yohancsx/MinionsStereoCamera/Images/arducamScrews.PNG

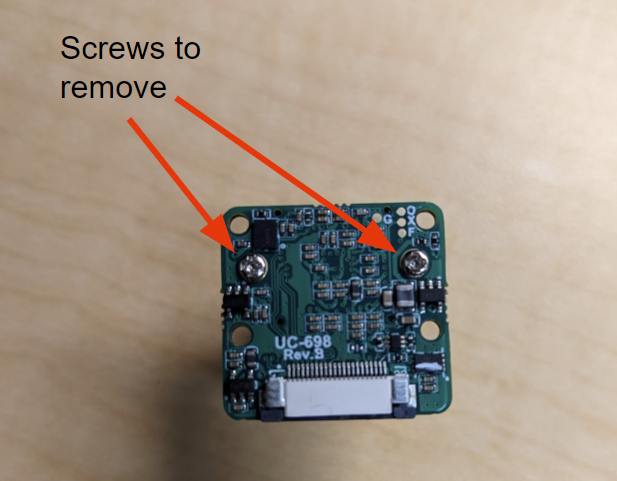
Images/arducamScrews.PNG
