yohancsx/MinionsStereoCamera/Images/cameraFilling.PNG

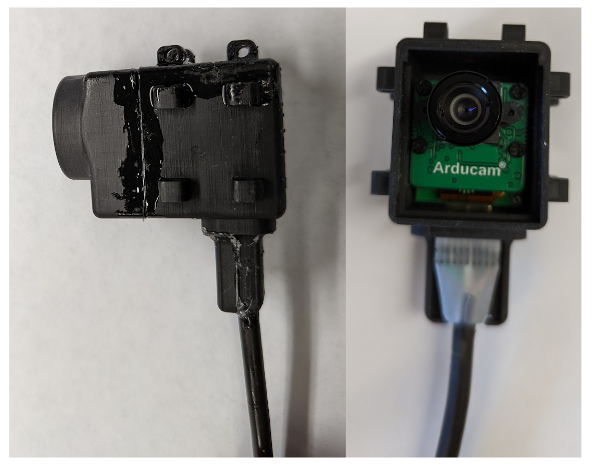
Images/cameraFilling.PNG
