yohancsx/MinionsStereoCamera/Images/housingDiagram.PNG

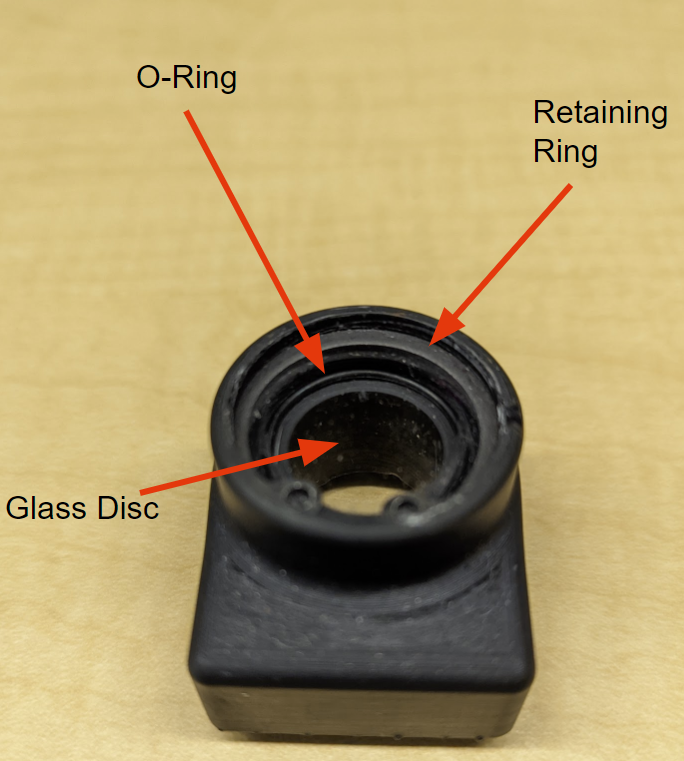
Images/housingDiagram.PNG
