yohancsx/MinionsStereoCamera/Images/lightFilling.PNG

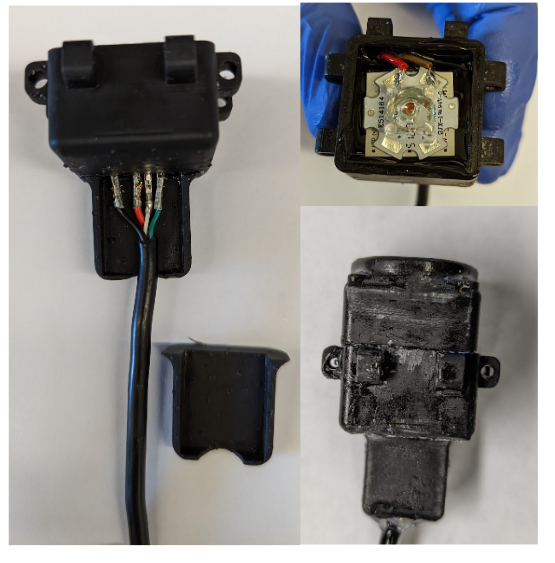
Images/lightFilling.PNG
