yohancsx/MinionsStereoCamera/Images/powerGroundDriver.PNG

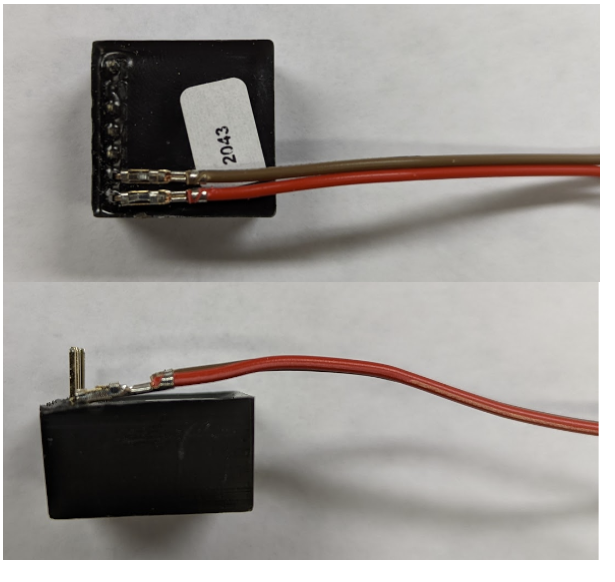
Images/powerGroundDriver.PNG
