yohancsx/MinionsStereoCamera/Images/PXL_20220421_215147885.jpg

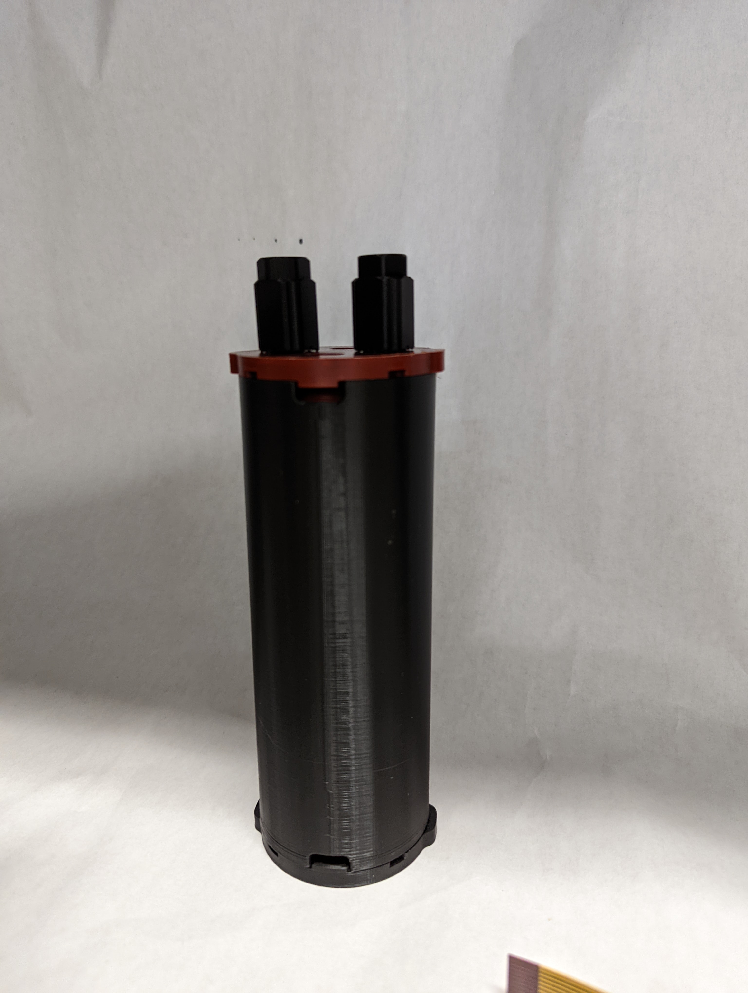
Images/PXL_20220421_215147885.jpg
