yohancsx/MinionsStereoCamera/Images/PXL_20220421_220706558.jpg

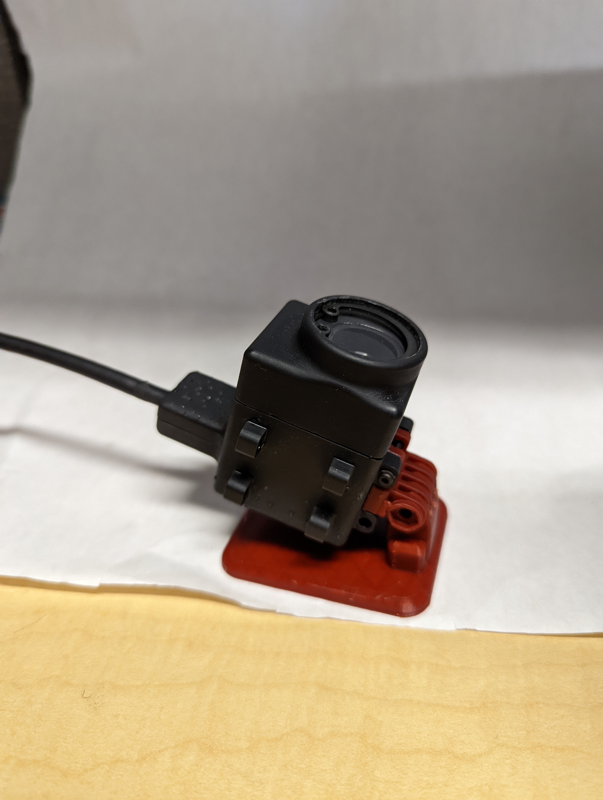
Images/PXL_20220421_220706558.jpg
