yohancsx/MinionsStereoCamera/Images/PXL_20220421_220925433.jpg

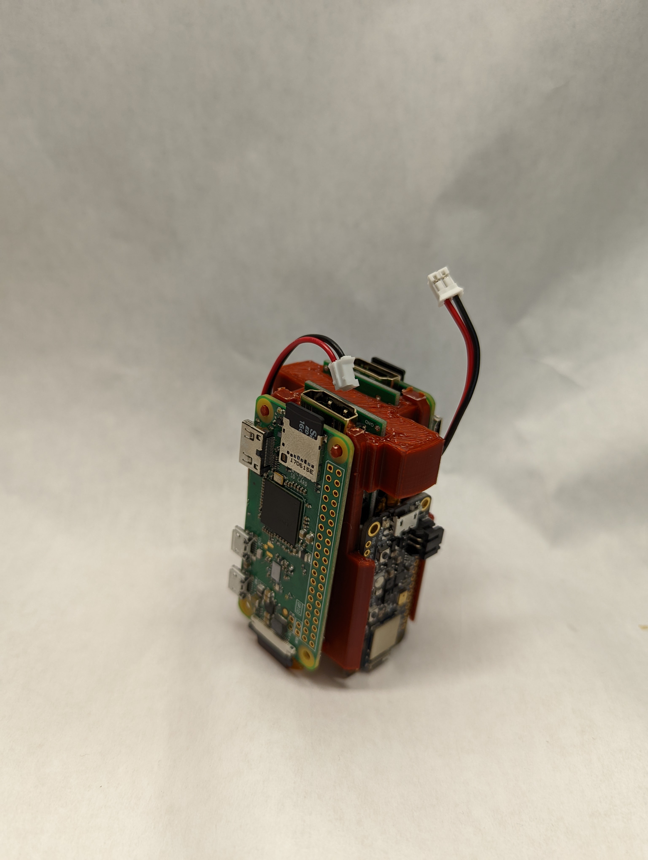
Images/PXL_20220421_220925433.jpg
