yohancsx/MinionsStereoCamera/Images/PXL_20220421_222905097.jpg

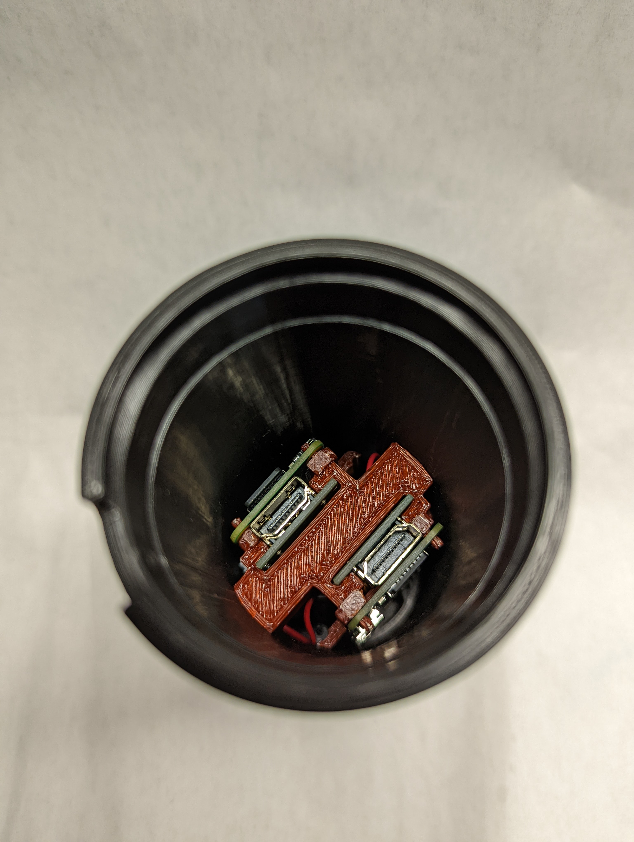
Images/PXL_20220421_222905097.jpg
