yohancsx/MinionsStereoCamera/Images/PXL_20220526_020410349.jpg

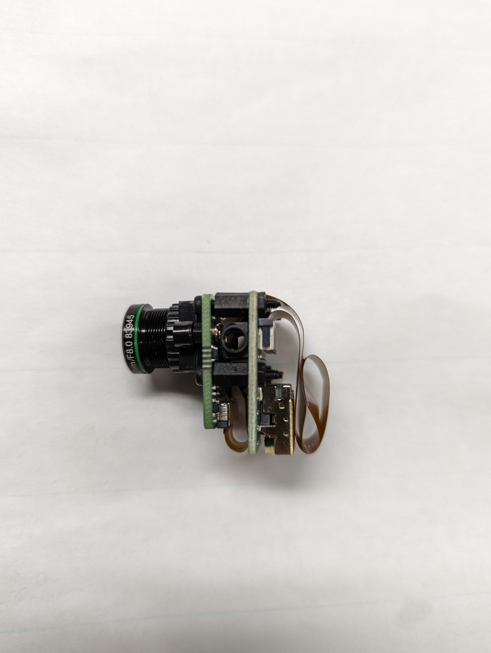
Images/PXL_20220526_020410349.jpg
