yohancsx/MinionsStereoCamera/Images/PXL_20220526_020418973.jpg

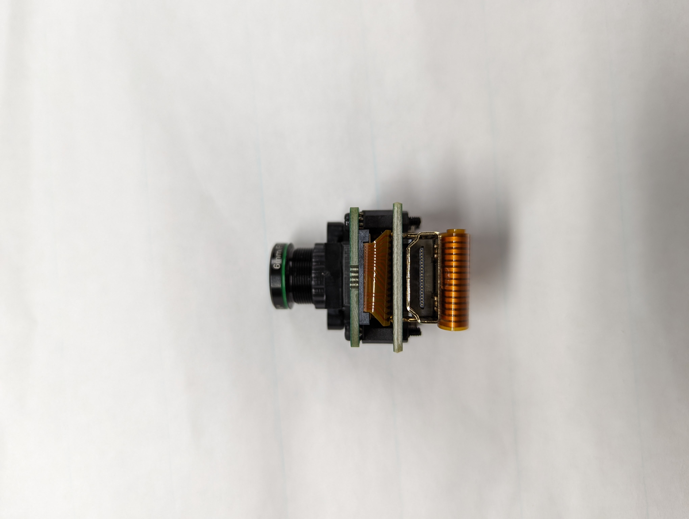
Images/PXL_20220526_020418973.jpg
