yohancsx/MinionsStereoCamera/Images/PXL_20220526_020445970.jpg

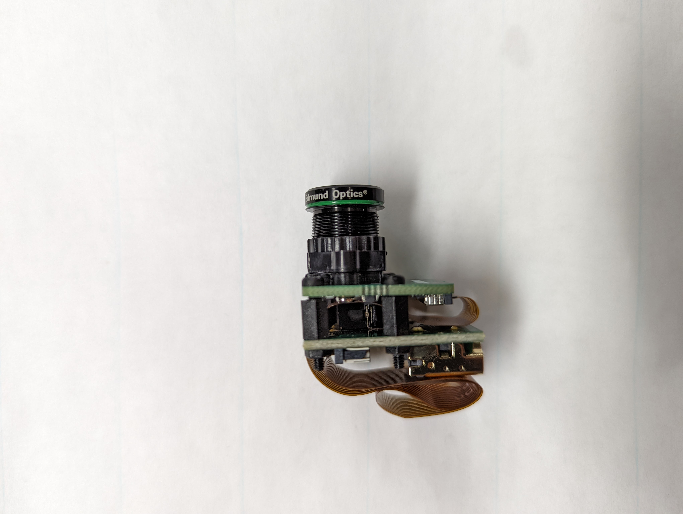
Images/PXL_20220526_020445970.jpg
