yohancsx/MinionsStereoCamera/Images/PXL_20220528_033501220.jpg

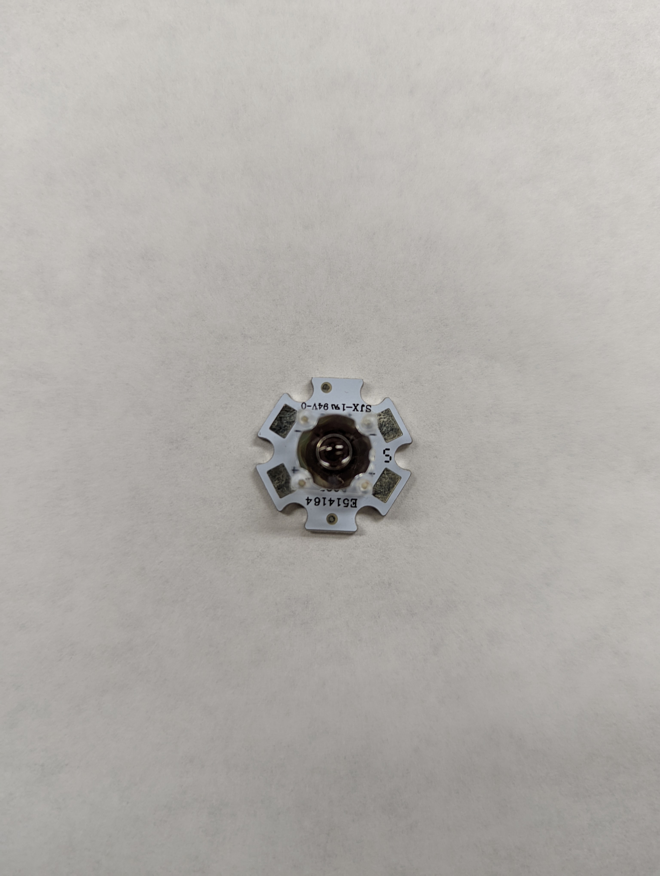
Images/PXL_20220528_033501220.jpg
