yohancsx/MinionsStereoCamera/Images/PXL_20220528_033528025.jpg

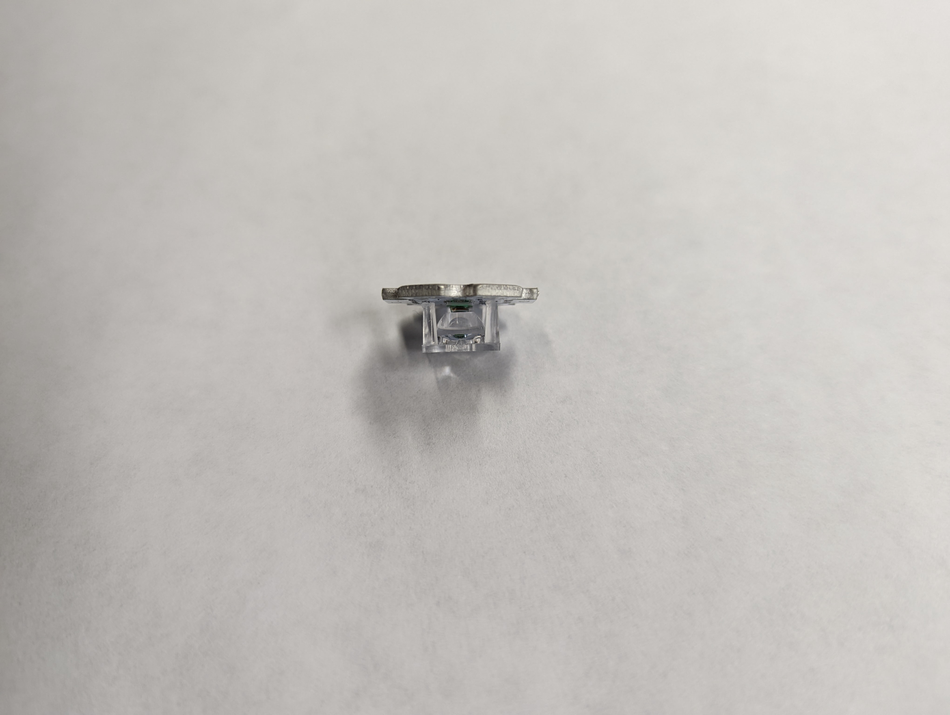
Images/PXL_20220528_033528025.jpg
