yohancsx/MinionsStereoCamera/Images/PXL_20220528_035723664.jpg

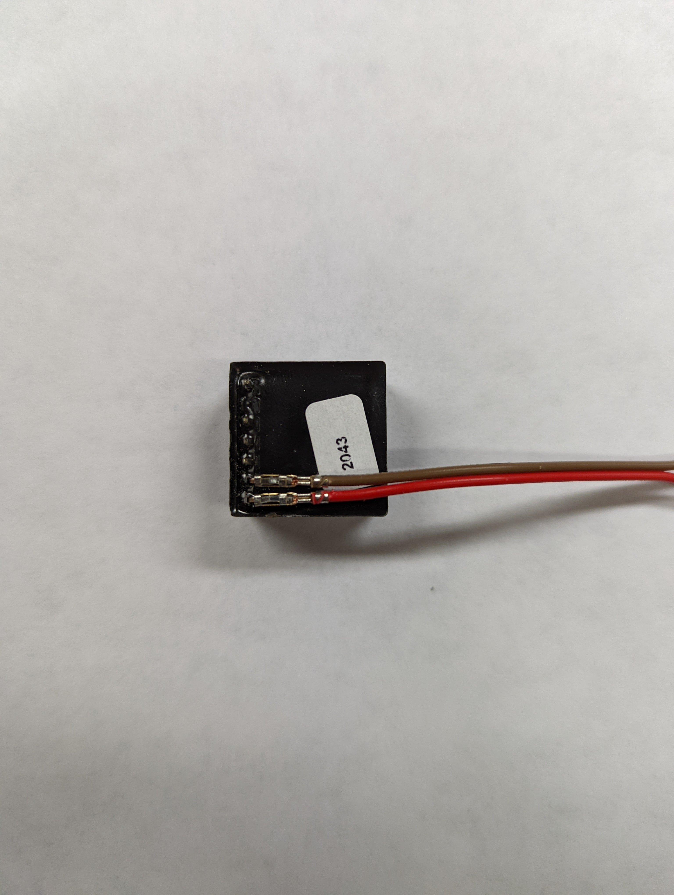
Images/PXL_20220528_035723664.jpg
