yohancsx/MinionsStereoCamera/Images/PXL_20220528_035728133.jpg

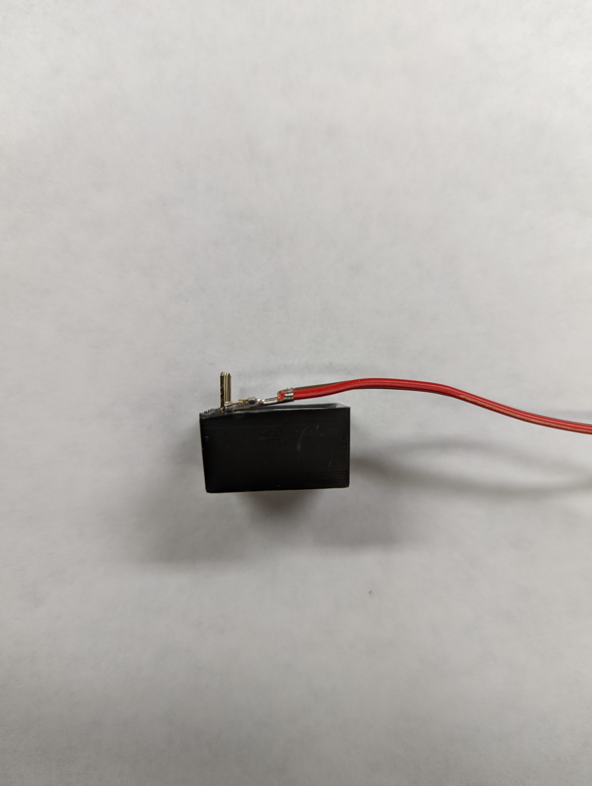
Images/PXL_20220528_035728133.jpg
