yohancsx/MinionsStereoCamera/Images/PXL_20220528_041638097.jpg

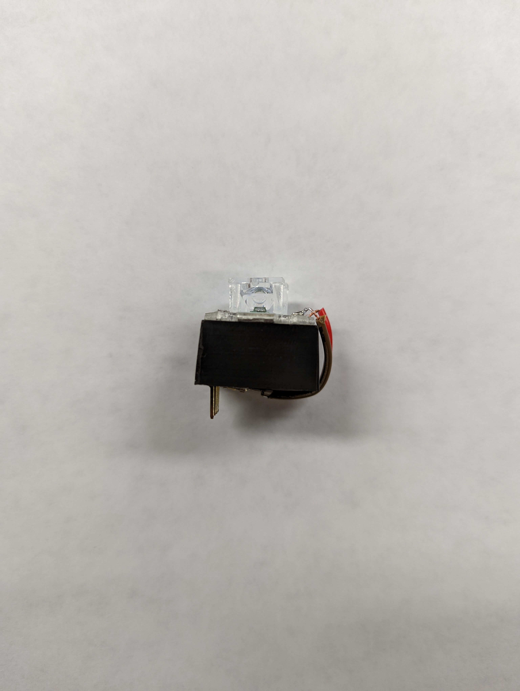
Images/PXL_20220528_041638097.jpg
