yohancsx/MinionsStereoCamera/Images/PXL_20220528_041642289.jpg

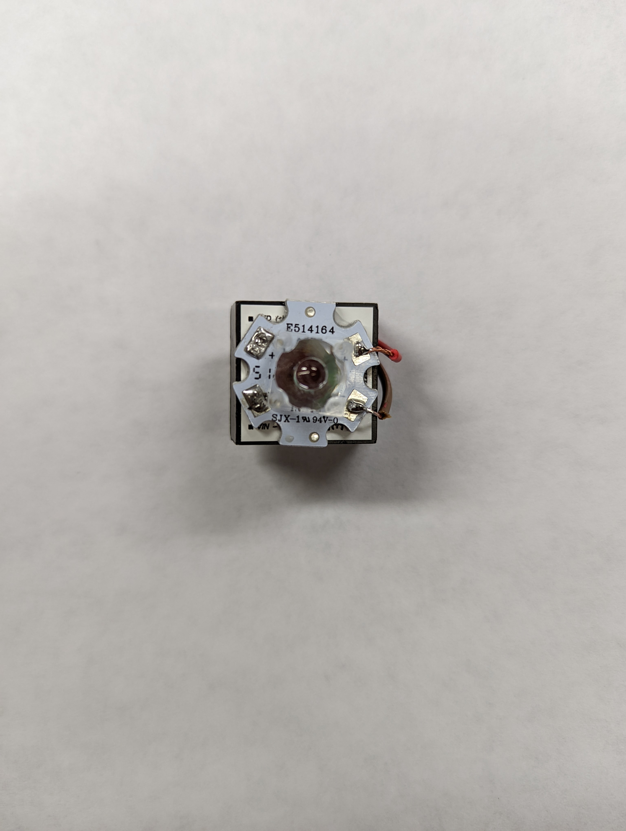
Images/PXL_20220528_041642289.jpg
