yohancsx/MinionsStereoCamera/Images/PXL_20220528_150322493.jpg

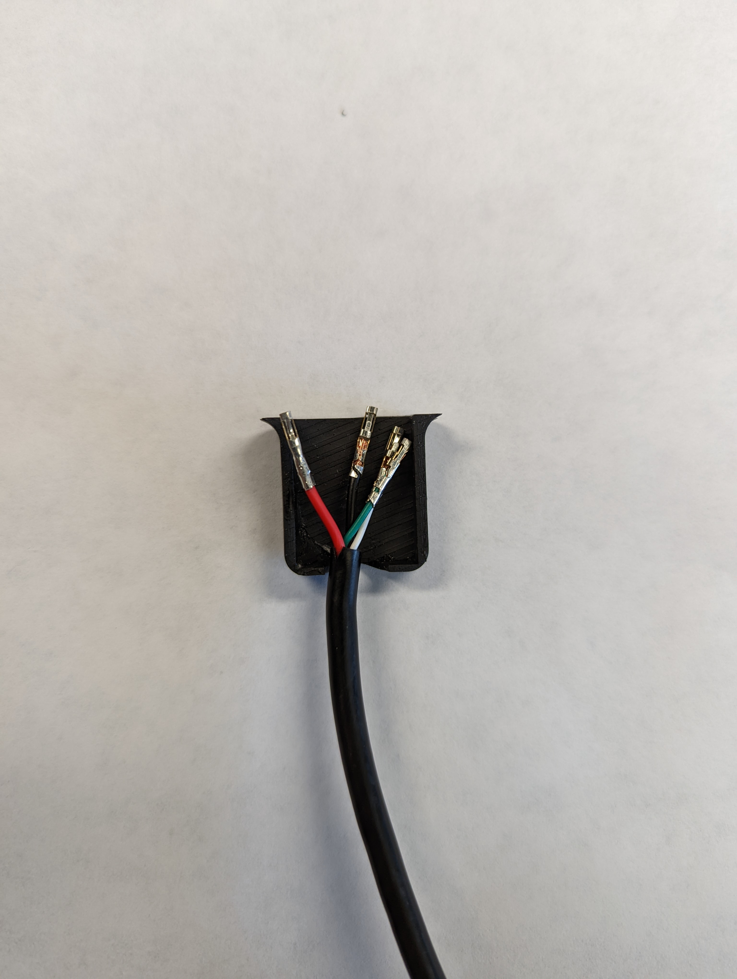
Images/PXL_20220528_150322493.jpg
