yohancsx/MinionsStereoCamera/Images/PXL_20220528_170543989.jpg

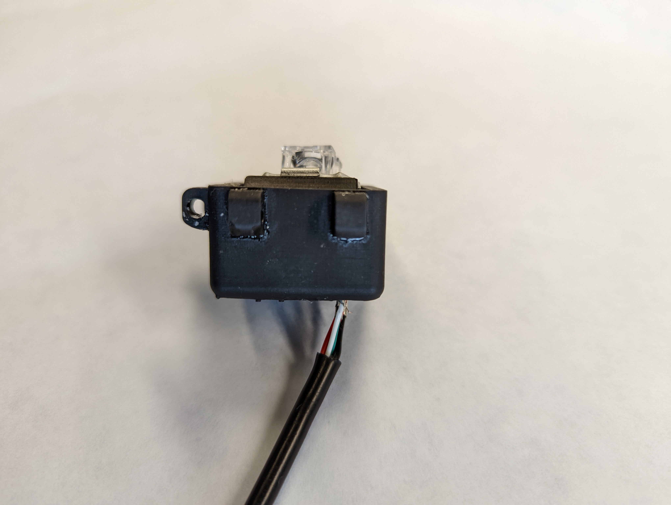
Images/PXL_20220528_170543989.jpg
