yohancsx/MinionsStereoCamera/Images/PXL_20220528_170554680.jpg

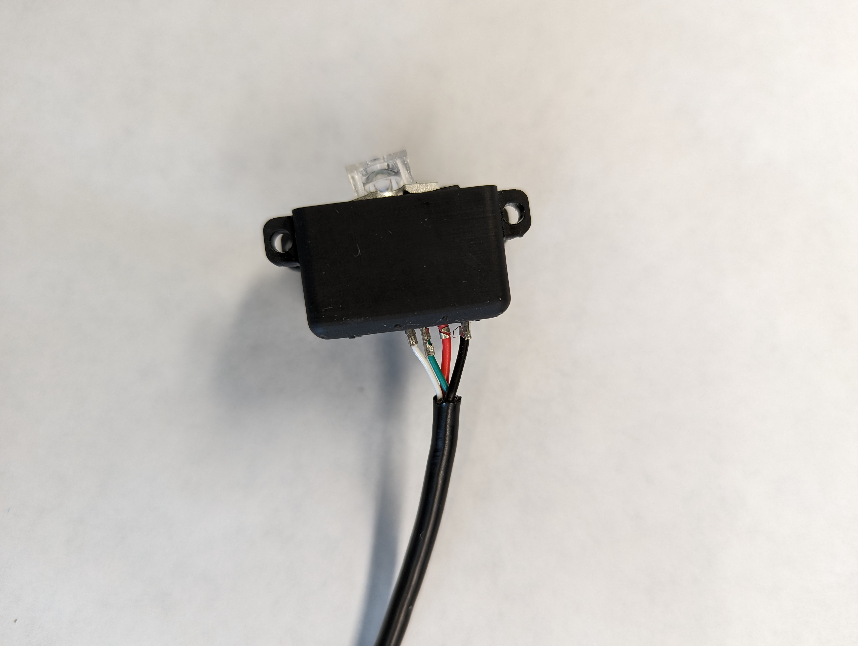
Images/PXL_20220528_170554680.jpg
