yohancsx/MinionsStereoCamera/Images/PXL_20220528_170604960.jpg

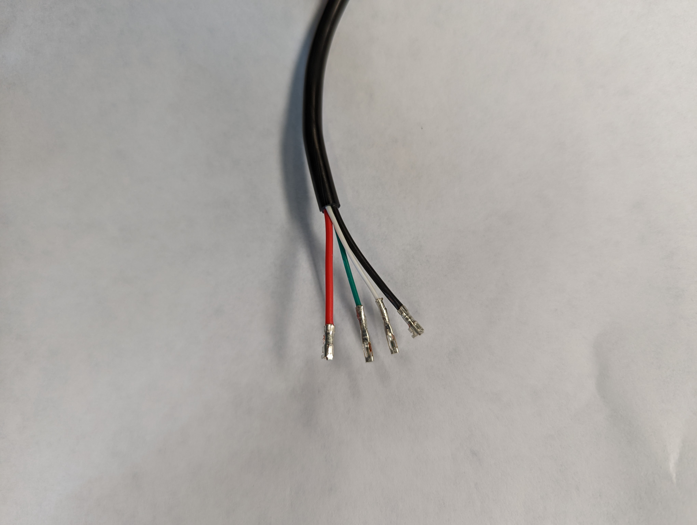
Images/PXL_20220528_170604960.jpg
