yohancsx/MinionsStereoCamera/Images/PXL_20220528_183940750.jpg

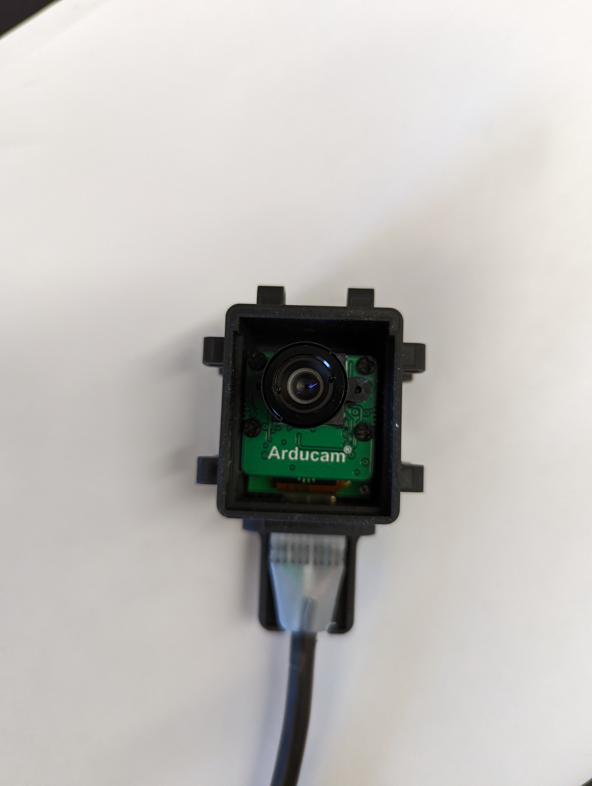
Images/PXL_20220528_183940750.jpg
