yohancsx/MinionsStereoCamera/Images/PXL_20220528_185714091.jpg

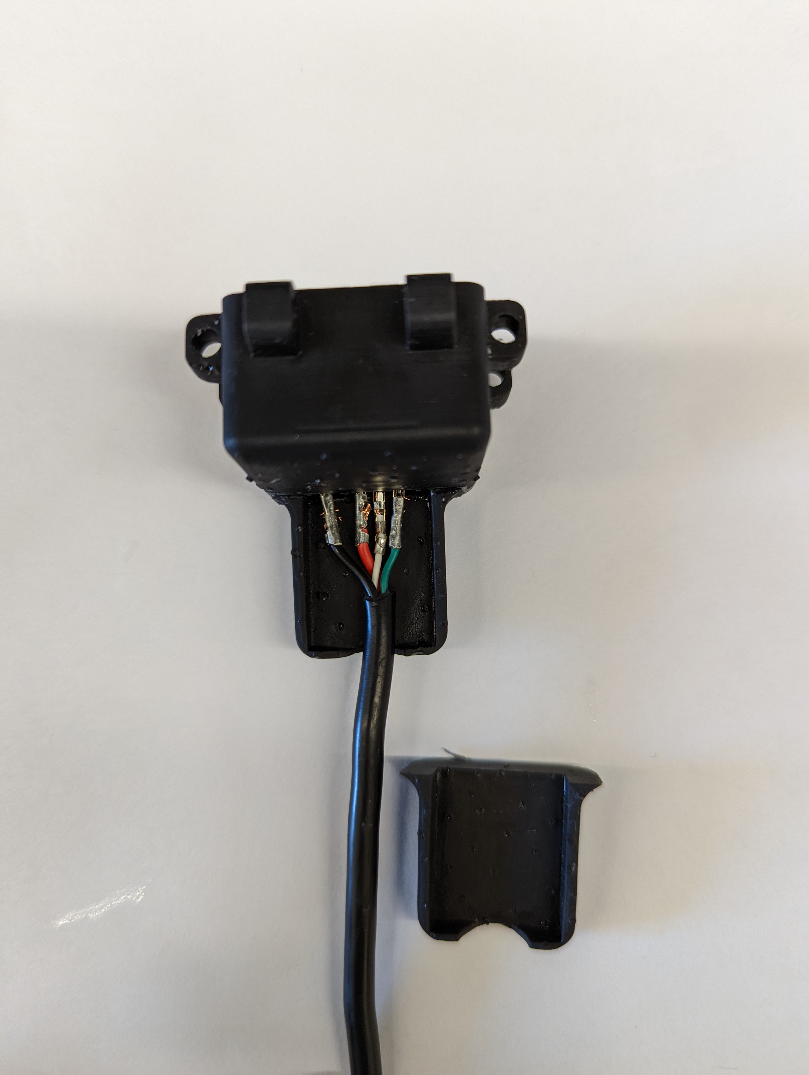
Images/PXL_20220528_185714091.jpg
