yohancsx/MinionsStereoCamera/Images/PXL_20220528_192507385.jpg

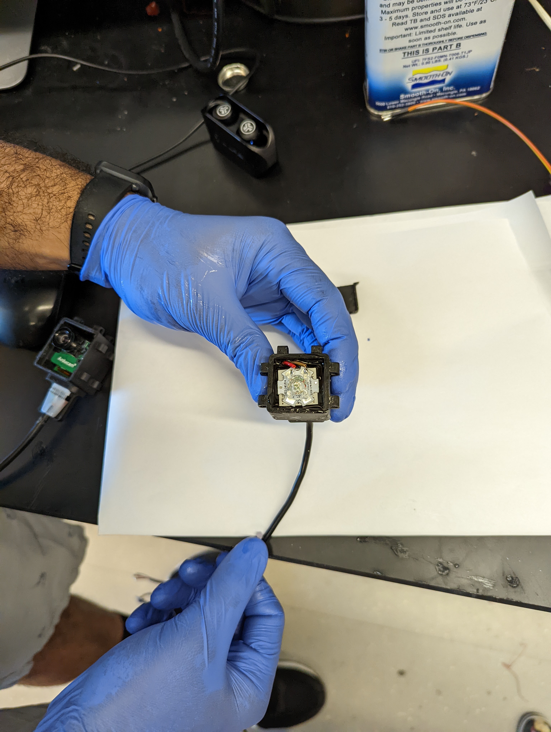
Images/PXL_20220528_192507385.jpg
