yohancsx/MinionsStereoCamera/Images/PXL_20220528_192509535.jpg

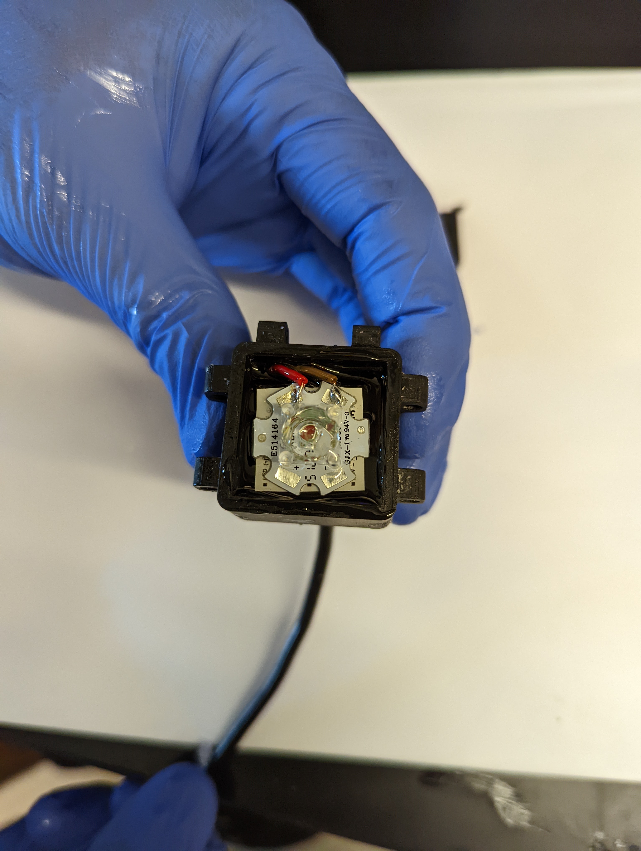
Images/PXL_20220528_192509535.jpg
