yohancsx/MinionsStereoCamera/Images/PXL_20220528_192511123.jpg

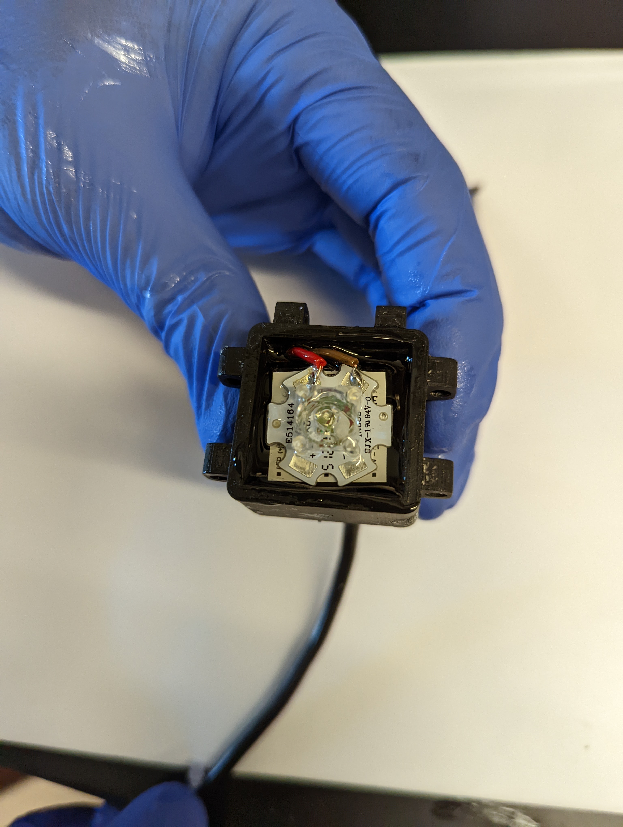
Images/PXL_20220528_192511123.jpg
