yohancsx/MinionsStereoCamera/Images/PXL_20220528_205123236.jpg

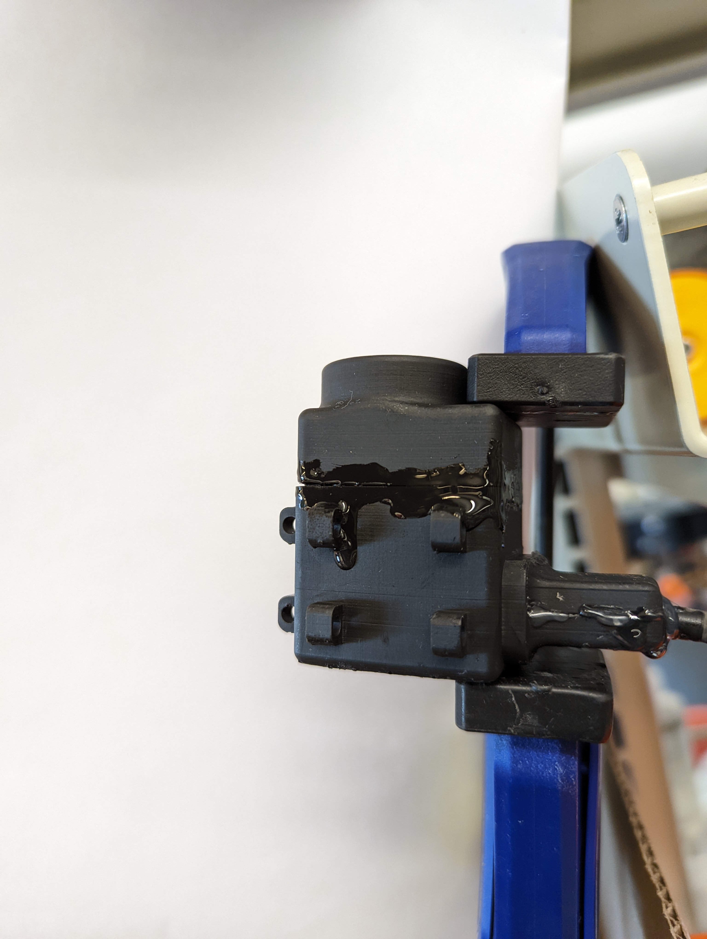
Images/PXL_20220528_205123236.jpg
