yohancsx/MinionsStereoCamera/Images/PXL_20220528_205125840.jpg

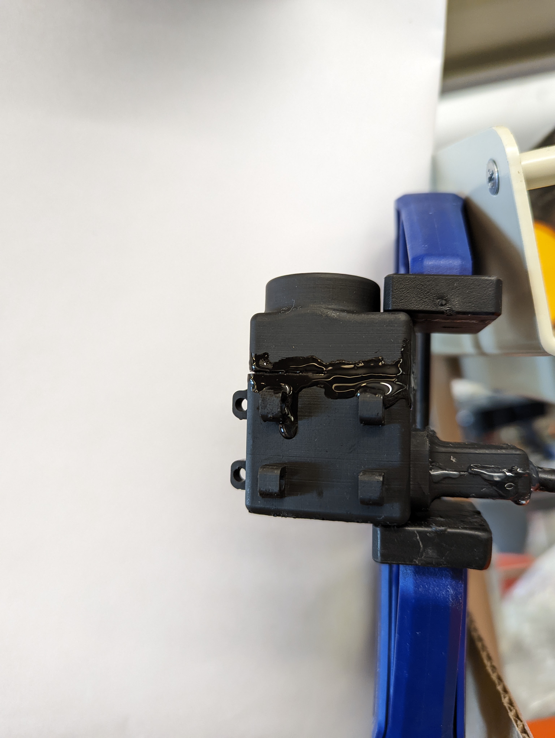
Images/PXL_20220528_205125840.jpg
