yohancsx/MinionsStereoCamera/Images/PXL_20220528_231235607.jpg

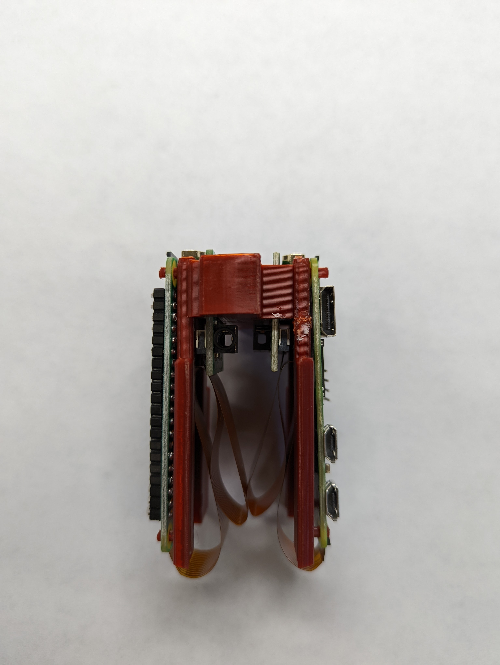
Images/PXL_20220528_231235607.jpg
