yohancsx/MinionsStereoCamera/Images/PXL_20220528_231241320.jpg

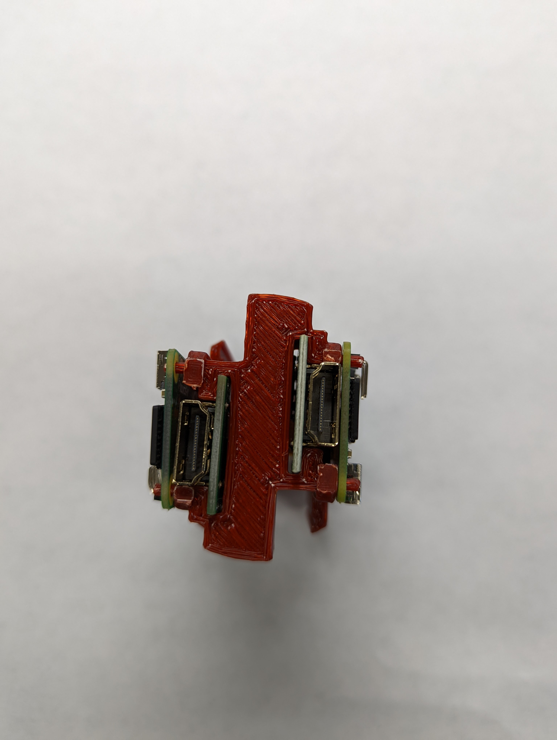
Images/PXL_20220528_231241320.jpg
