yohancsx/MinionsStereoCamera/Images/PXL_20220528_231245960.jpg

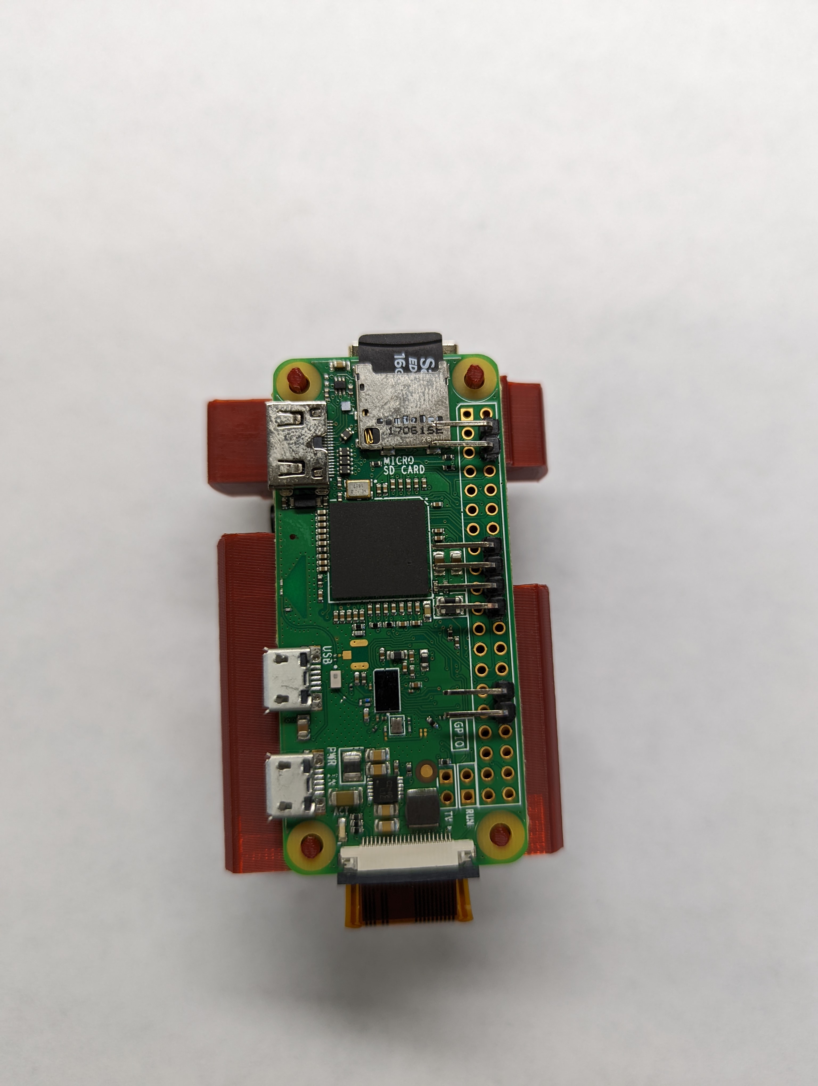
Images/PXL_20220528_231245960.jpg
