yohancsx/MinionsStereoCamera/Images/PXL_20220528_231329349.jpg

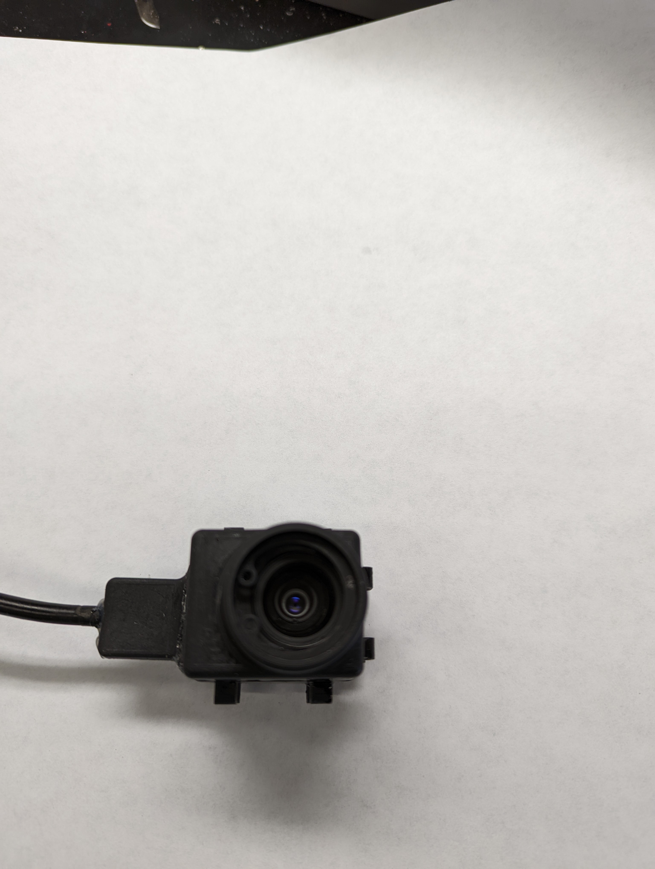
Images/PXL_20220528_231329349.jpg
