yohancsx/MinionsStereoCamera/Images/PXL_20220528_231333550.jpg

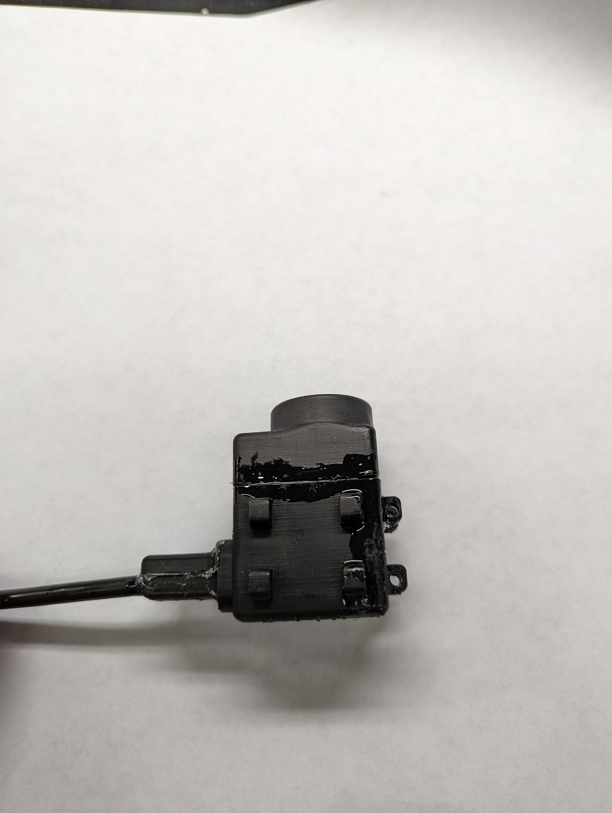
Images/PXL_20220528_231333550.jpg
