yohancsx/MinionsStereoCamera/Images/PXL_20220528_231343680.jpg

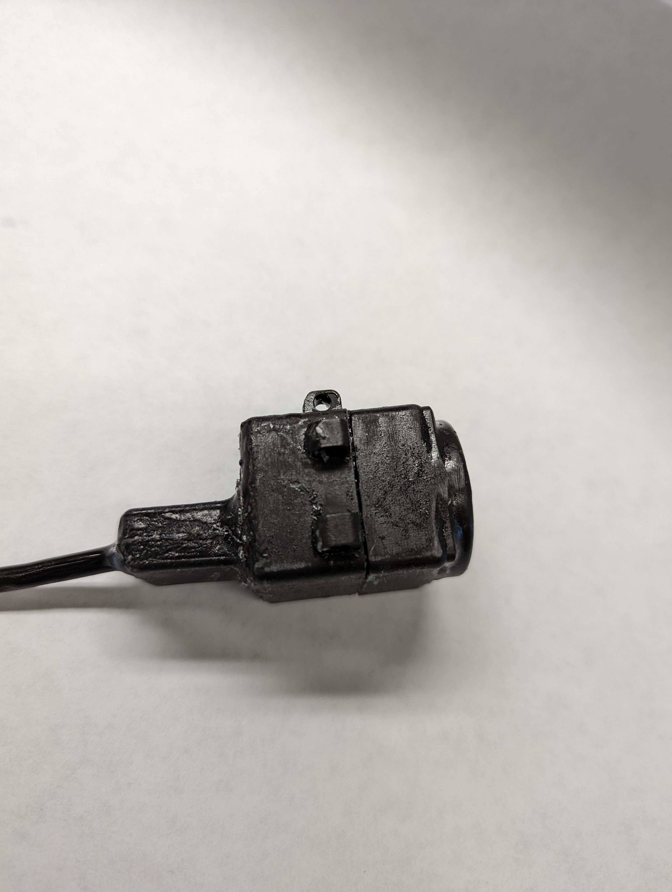
Images/PXL_20220528_231343680.jpg
