yohancsx/MinionsStereoCamera/Images/PXL_20220528_231351087.jpg

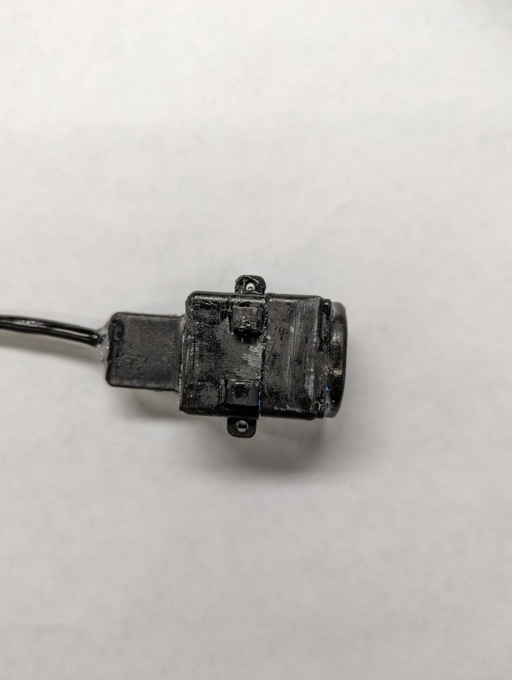
Images/PXL_20220528_231351087.jpg
