yohancsx/MinionsStereoCamera/Images/PXL_20220529_000241361.jpg

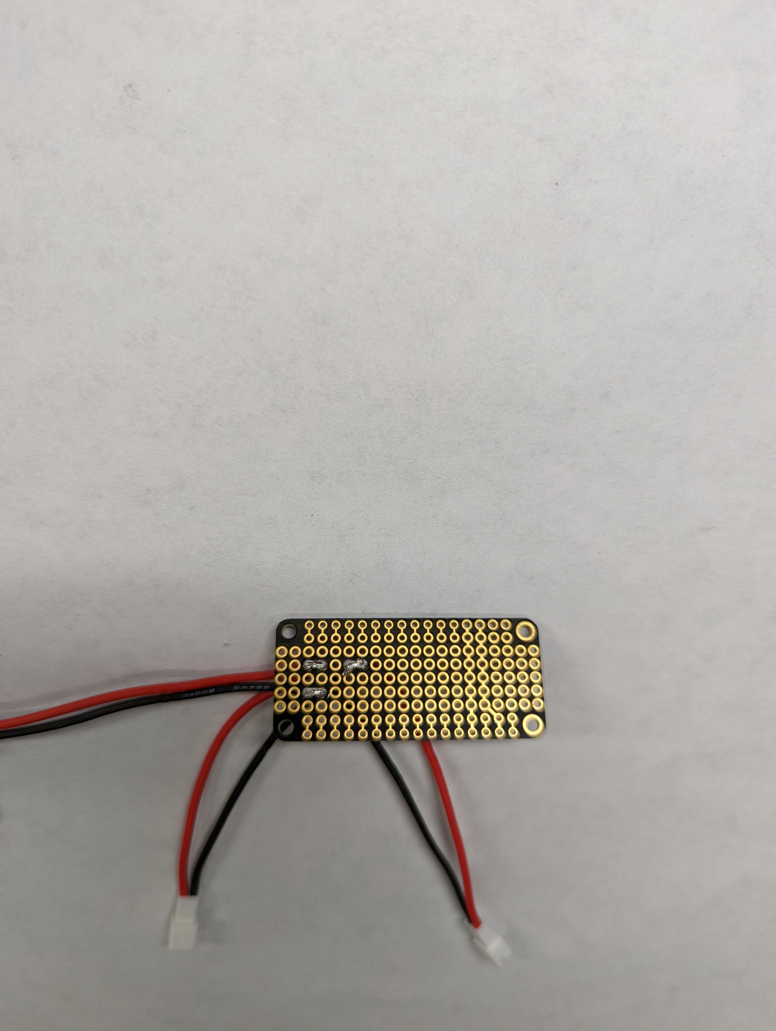
Images/PXL_20220529_000241361.jpg
