yohancsx/MinionsStereoCamera/Images/PXL_20220529_000252834.jpg

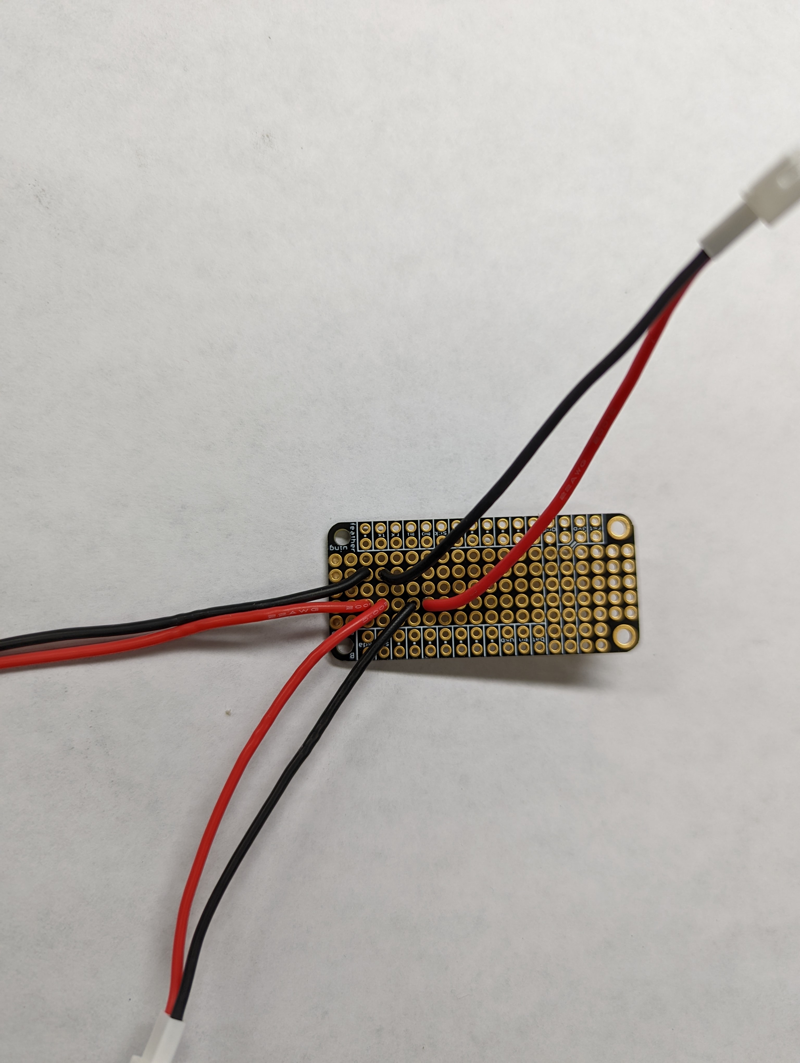
Images/PXL_20220529_000252834.jpg
