yohancsx/MinionsStereoCamera/Images/PXL_20220529_001251928.jpg

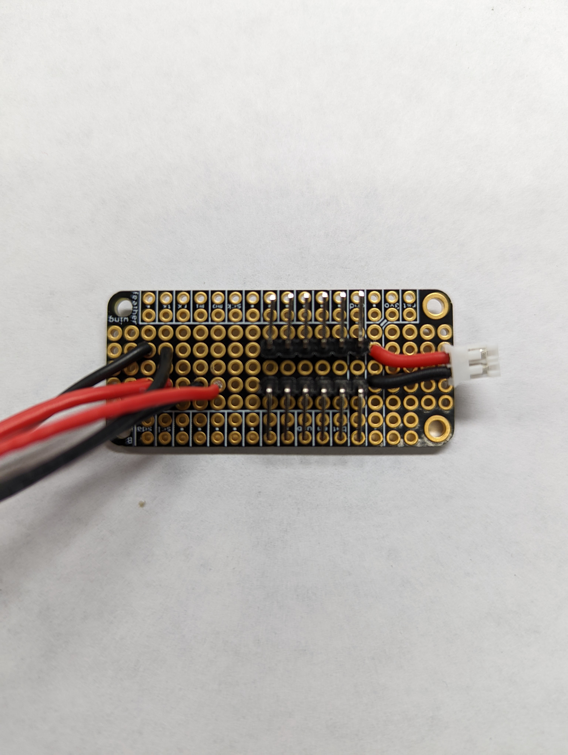
Images/PXL_20220529_001251928.jpg
