yohancsx/MinionsStereoCamera/Images/PXL_20220529_001300634.jpg

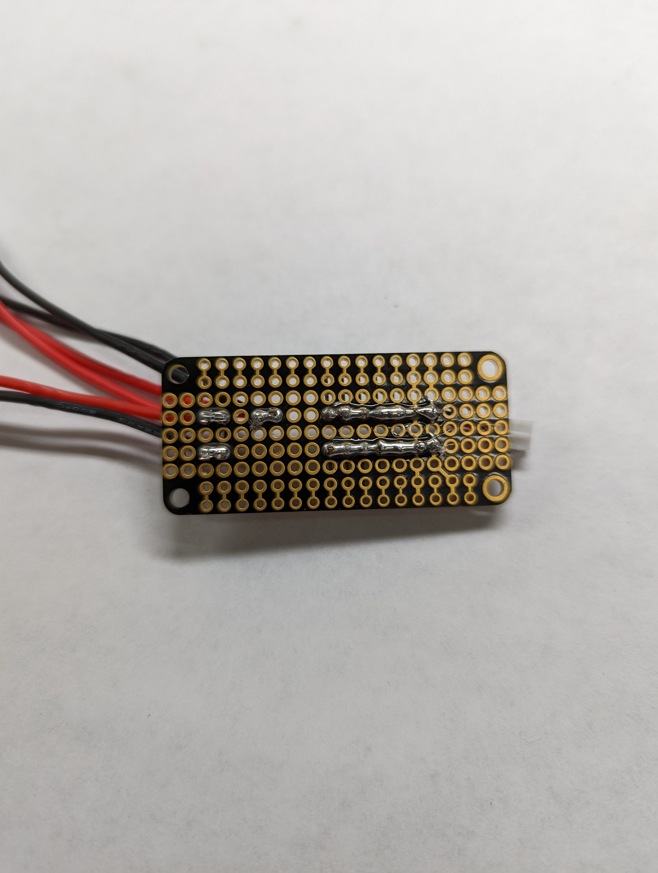
Images/PXL_20220529_001300634.jpg
