yohancsx/MinionsStereoCamera/Images/PXL_20220529_001824853.jpg

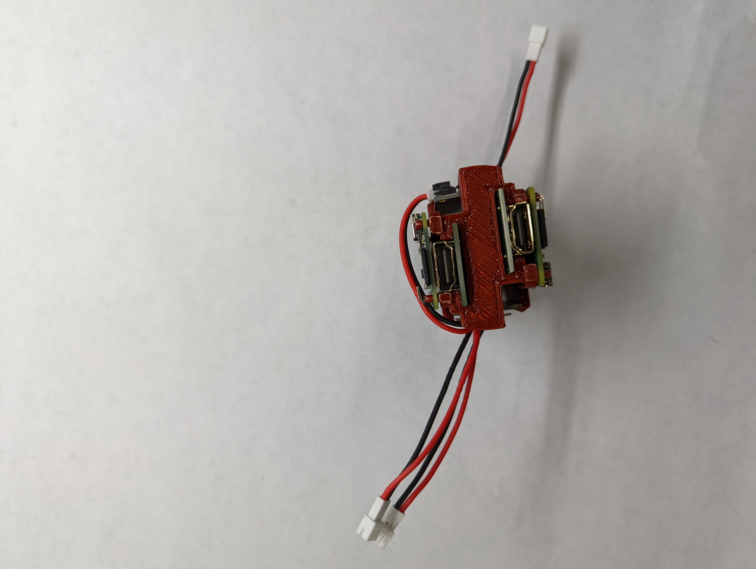
Images/PXL_20220529_001824853.jpg
