yohancsx/MinionsStereoCamera/Images/PXL_20220529_001828318.jpg

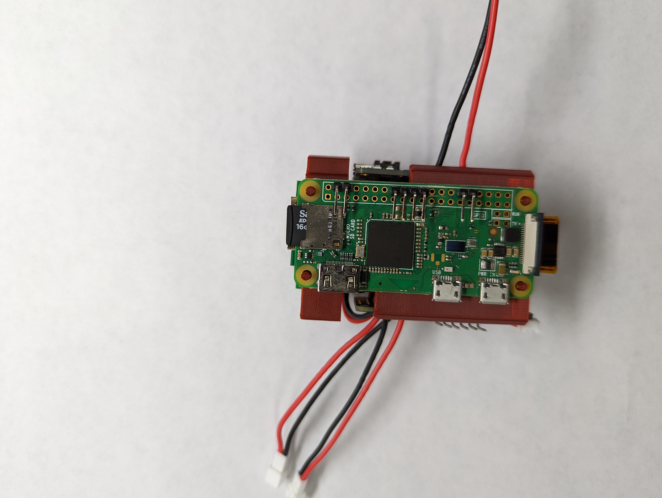
Images/PXL_20220529_001828318.jpg
