yohancsx/MinionsStereoCamera/Images/PXL_20220529_001835572.jpg

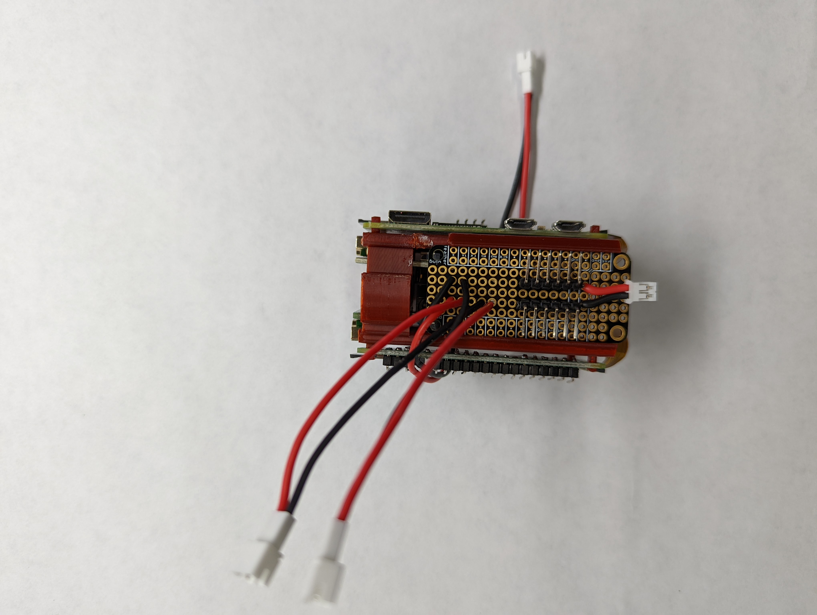
Images/PXL_20220529_001835572.jpg
