yohancsx/MinionsStereoCamera/Images/PXL_20220529_001842376.jpg

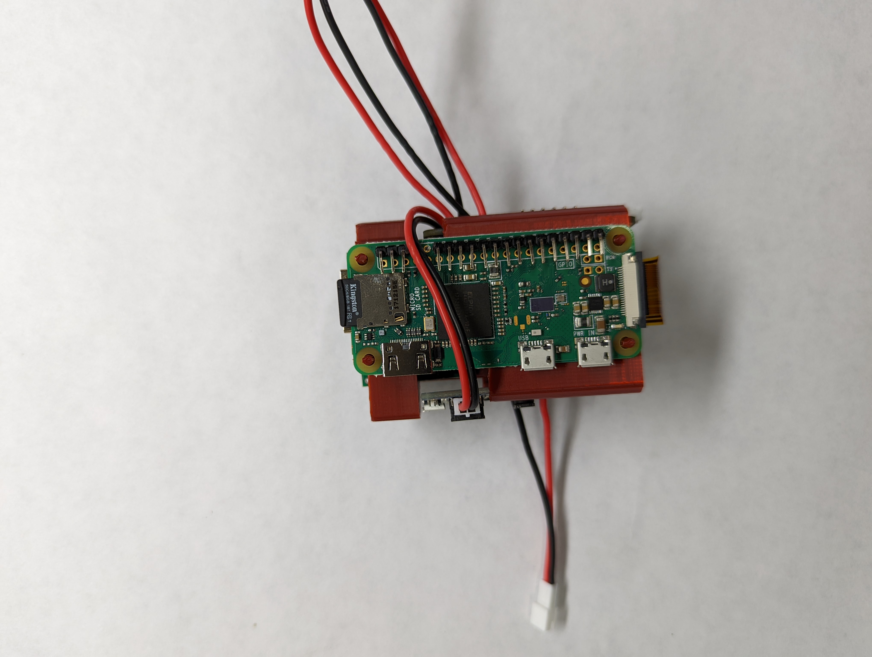
Images/PXL_20220529_001842376.jpg
