yohancsx/MinionsStereoCamera/Images/PXL_20220529_002021898.jpg

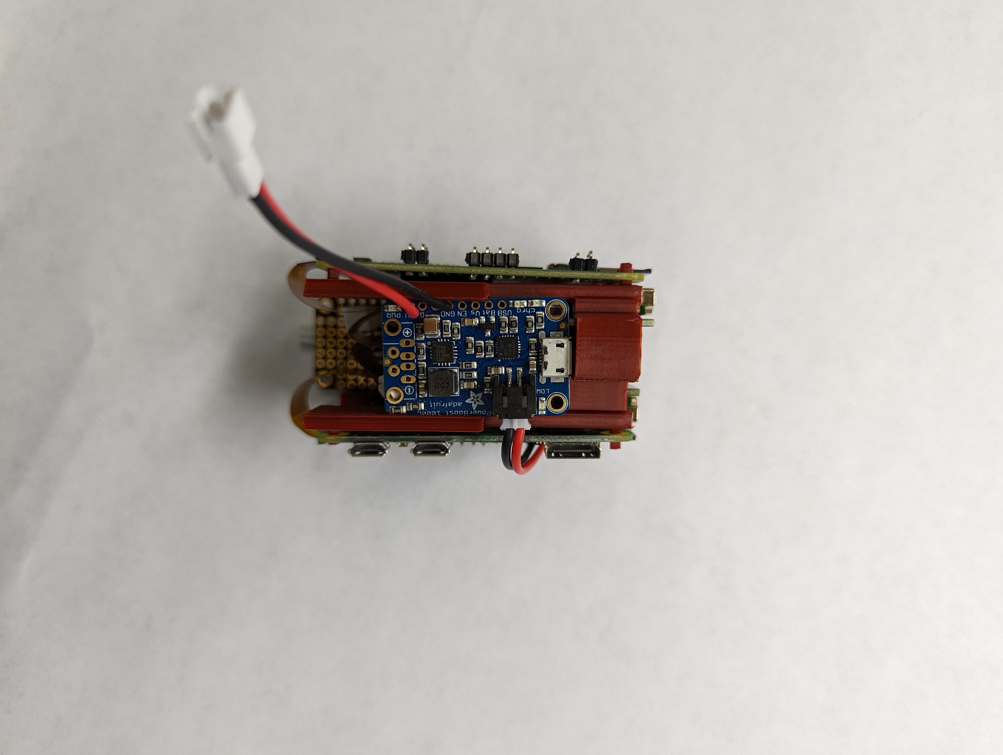
Images/PXL_20220529_002021898.jpg
