yohancsx/MinionsStereoCamera/Images/PXL_20220529_012648592.jpg

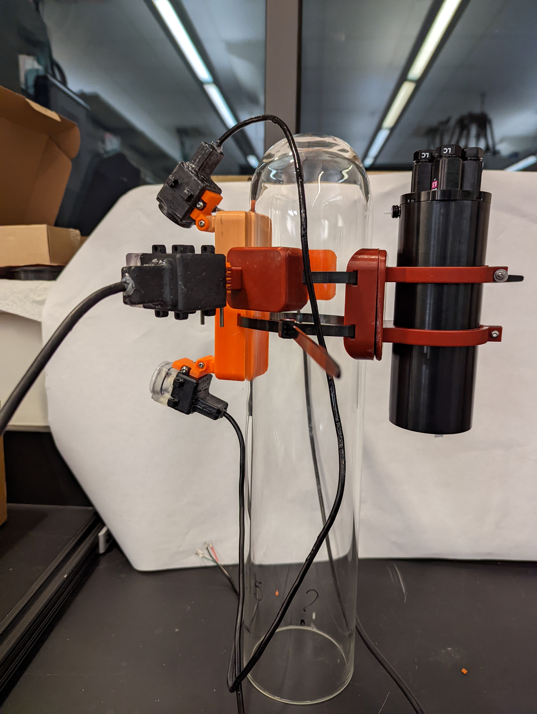
Images/PXL_20220529_012648592.jpg
