yohancsx/MinionsStereoCamera/Images/PXL_20220529_012657308.jpg

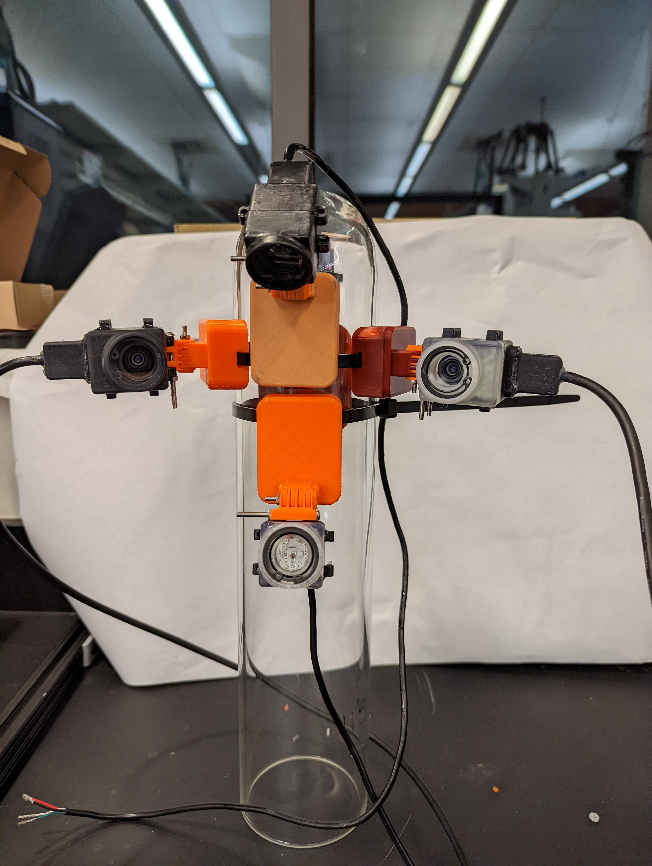
Images/PXL_20220529_012657308.jpg
