yohancsx/MinionsStereoCamera/CAD/Print Files/Light/Carclo Spacer.3mf

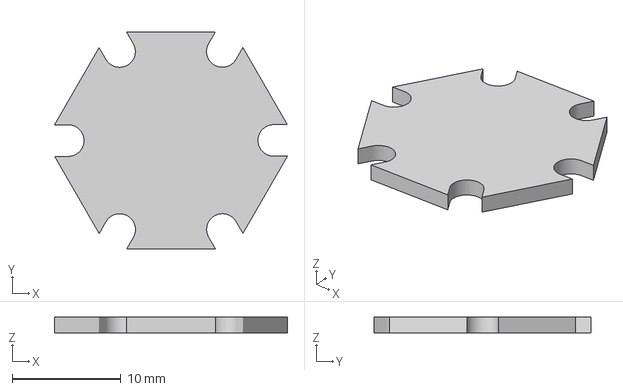
[picture p80: CAD file, 2022-09-15]
CAD/Print Files/Light/Carclo Spacer.3mf
21.4 x 20.0 x 1.45 mm
