yohancsx/MinionsStereoCamera/CAD/Fusion360 CAD/Stereocam Final_Light Housing v1.step

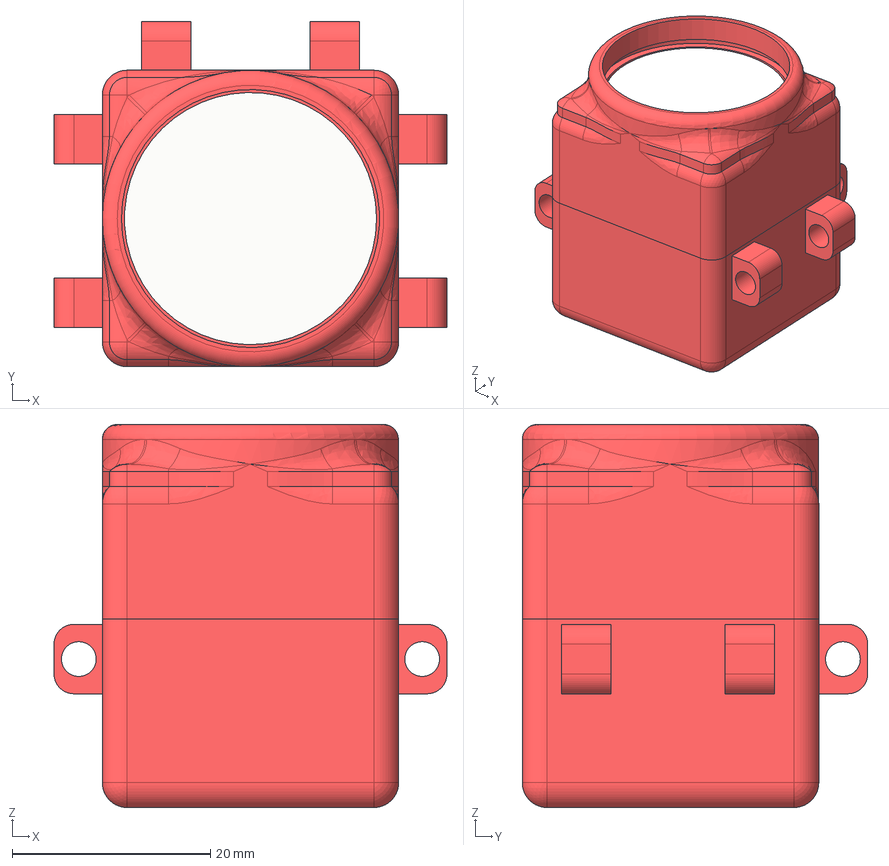
[picture p81: CAD file, 2022-09-14]
CAD/Fusion360 CAD/Stereocam Final_Light Housing v1.step
39.6 x 34.8 x 38.6 mm
Cree LED plate
10413_iss2_041007
2500-00565C
2500-00565C-BT
2500-00565C-SBN
2500-00565C-SB
2610-00066-DOME
8477K21_Borosilicate Glass Disc
9262K617_Oil-Resistant Buna-N O-Ring
