yohancsx/MinionsStereoCamera/CAD/Print Files/Camera/HDMI Spacer.3mf

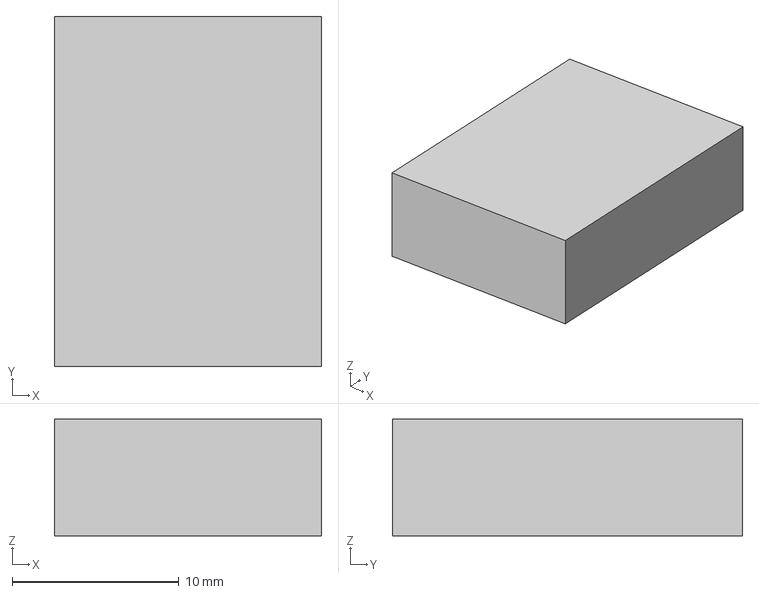
[picture p82: CAD file, 2022-09-15]
CAD/Print Files/Camera/HDMI Spacer.3mf
16.0 x 21.0 x 7.00 mm
