yohancsx/MinionsStereoCamera/Images/lightWiring.PNG

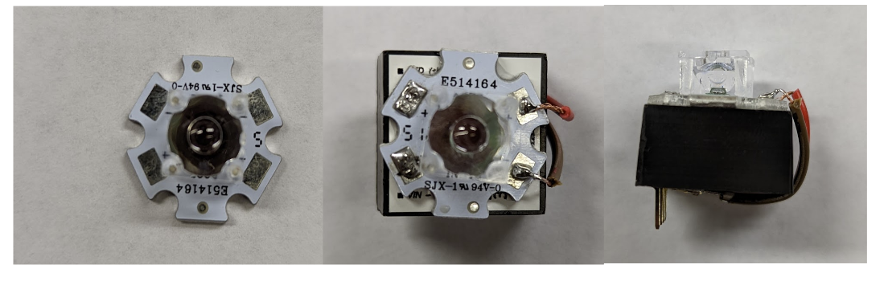
Images/lightWiring.PNG
