yohancsx/MinionsStereoCamera/Images/minionPicCADAssembly.PNG

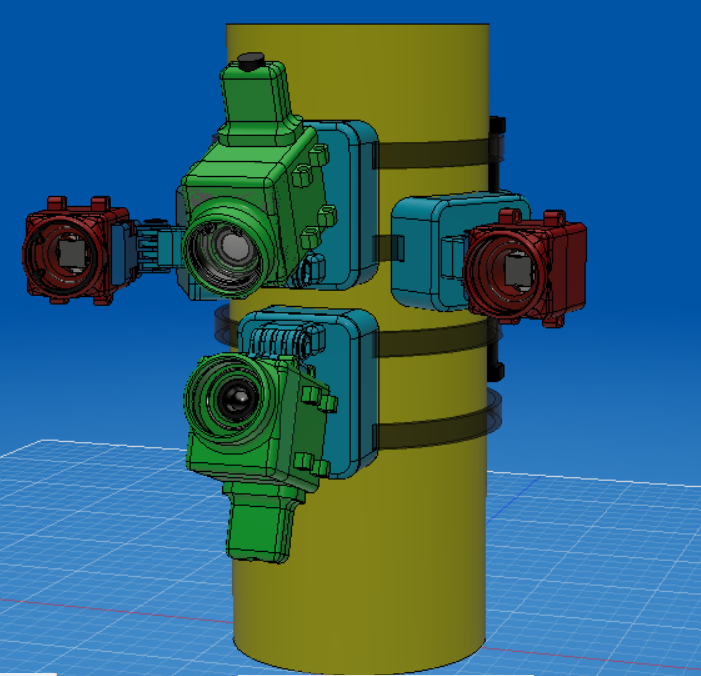
Images/minionPicCADAssembly.PNG
