yohancsx/MinionsStereoCamera/Images/powerSetup1.PNG

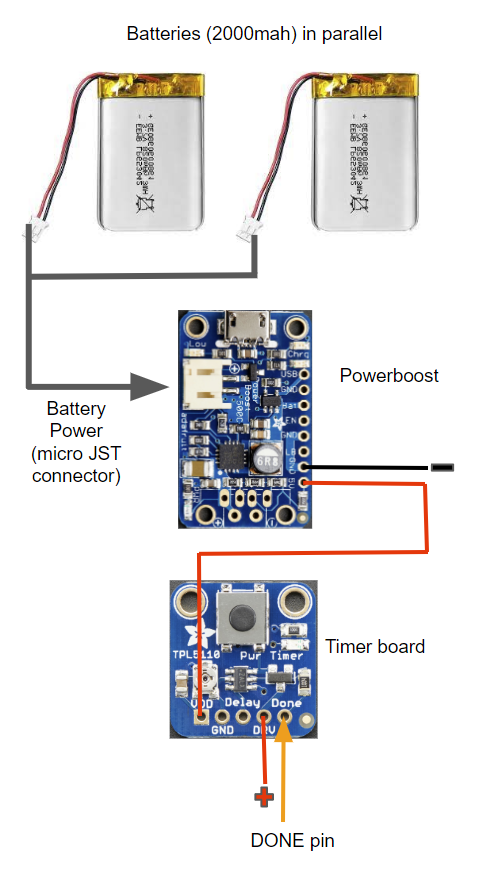
Images/powerSetup1.PNG
