yohancsx/MinionsStereoCamera/Images/powerSetup2.PNG

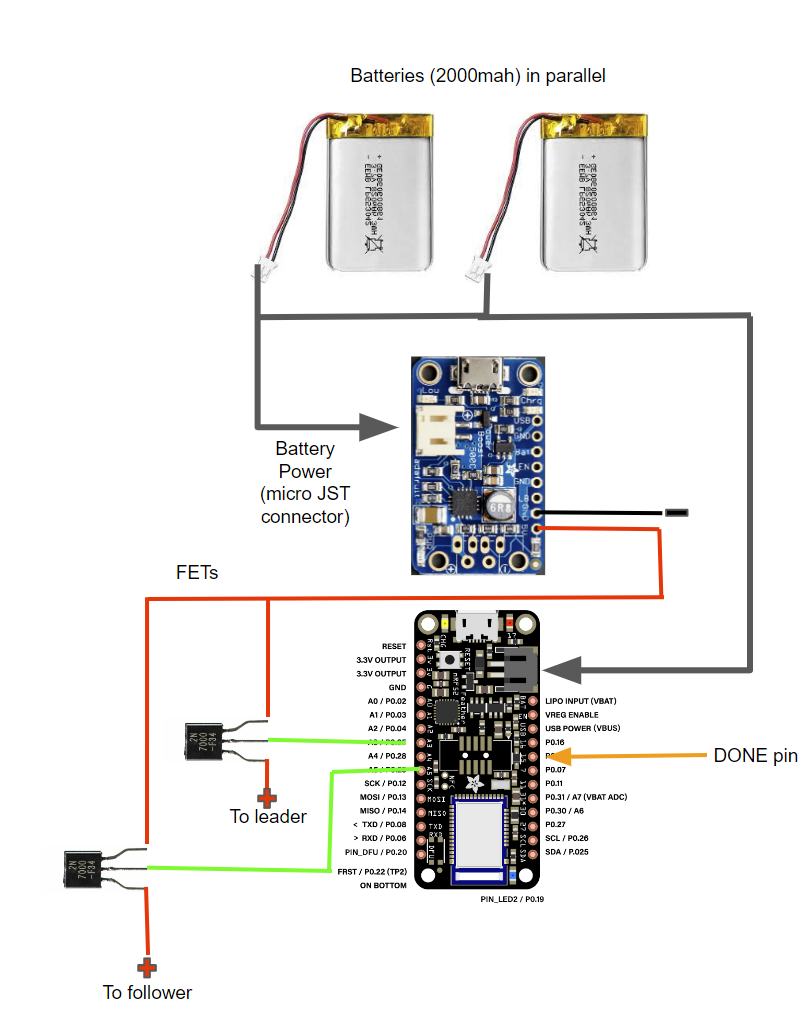
Images/powerSetup2.PNG
