yohancsx/MinionsStereoCamera/Images/print_orientation_housings.PNG

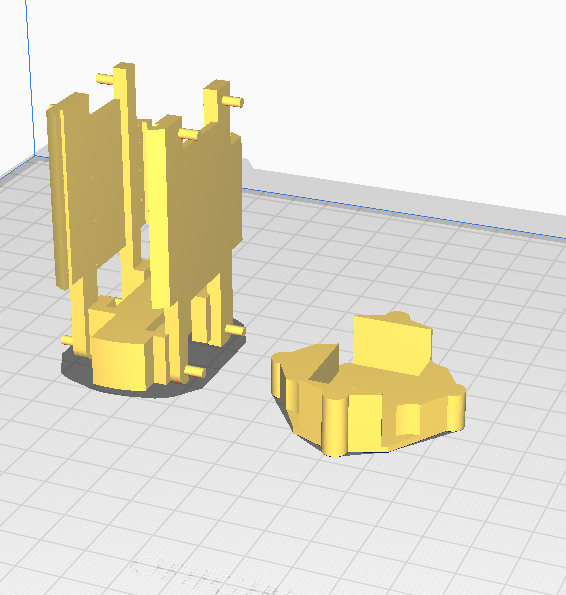
Images/print_orientation_housings.PNG
