yohancsx/MinionsStereoCamera/Images/print_orientation_M3_mounts.PNG

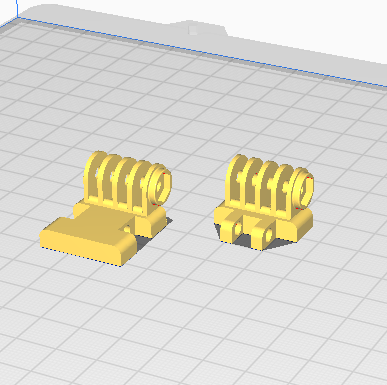
Images/print_orientation_M3_mounts.PNG
