yohancsx/MinionsStereoCamera/Images/print_orientation_mounts.PNG

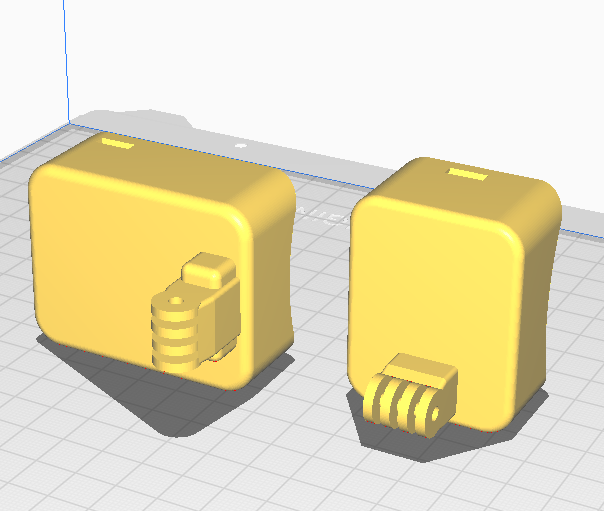
Images/print_orientation_mounts.PNG
